dfarley1/SPOT/CAD/Ping Sensor/ultrasonic.JPG

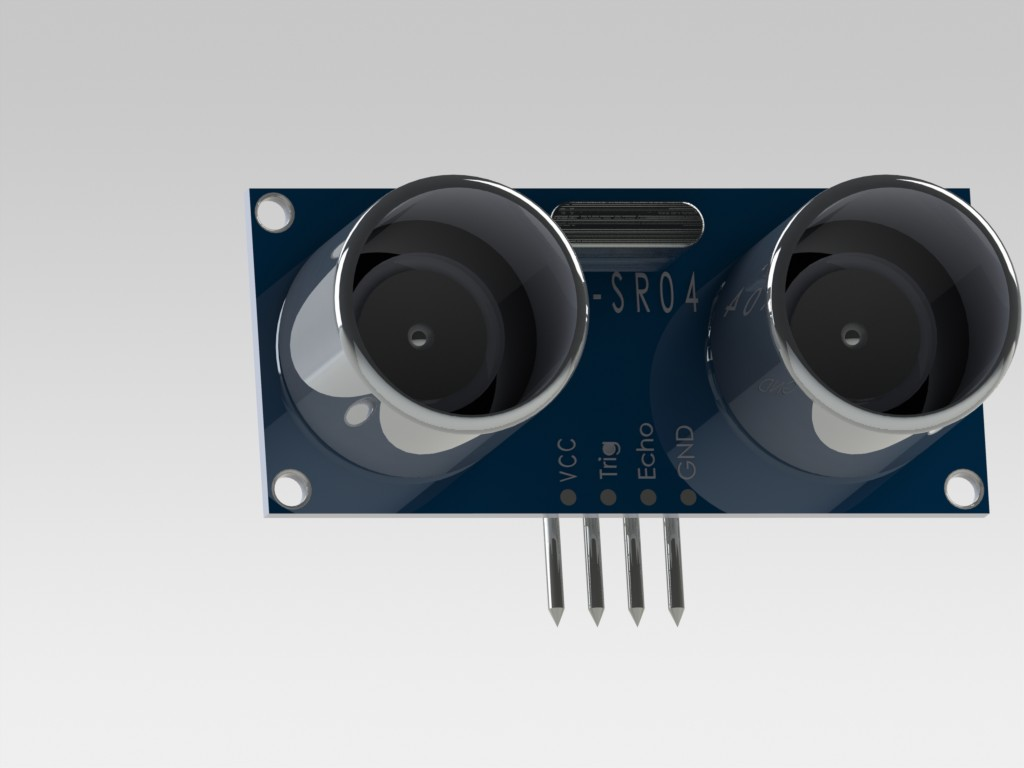
CAD/Ping Sensor/ultrasonic.JPG
