dfarley1/SPOT/CV/Pictures/Leopard/4YFD116.png

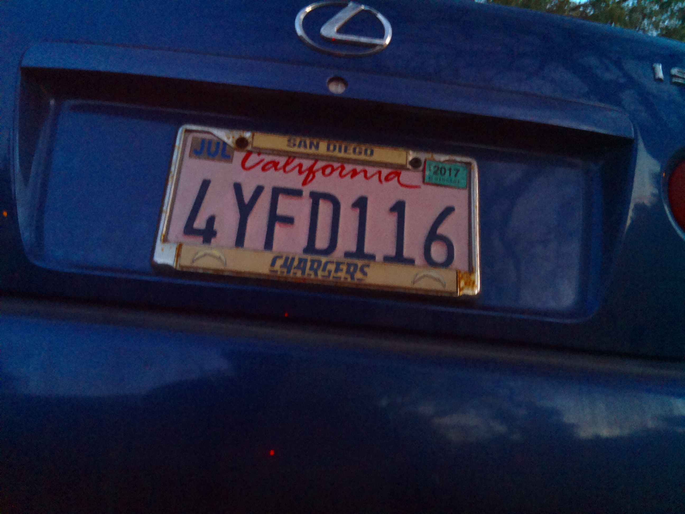
CV/Pictures/Leopard/4YFD116.png
