dfarley1/SPOT/CV/Pictures/Leopard/7FHW353.png

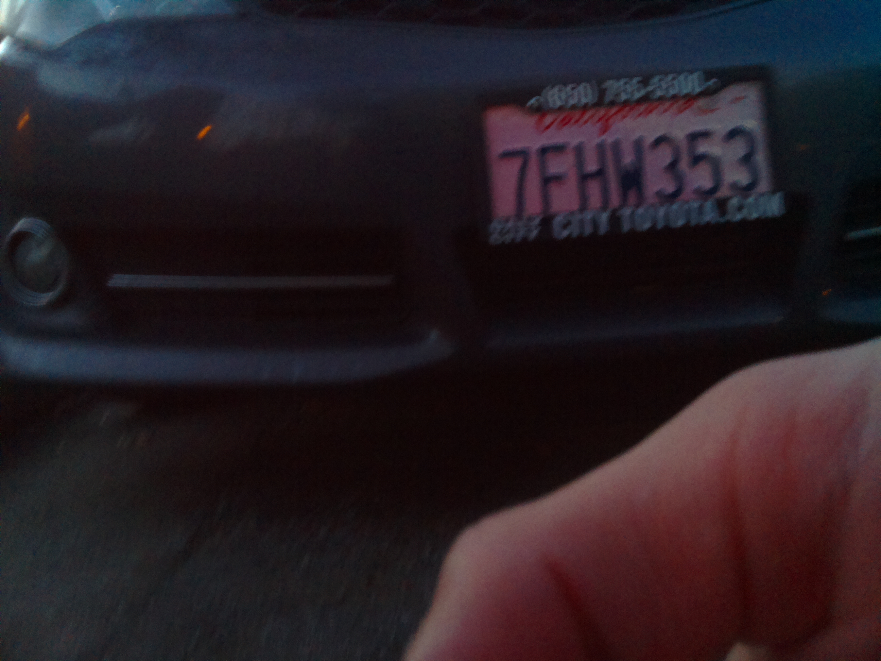
CV/Pictures/Leopard/7FHW353.png
