dfarley1/SPOT/CV/Pictures/Leopard/7FHW353_2.png

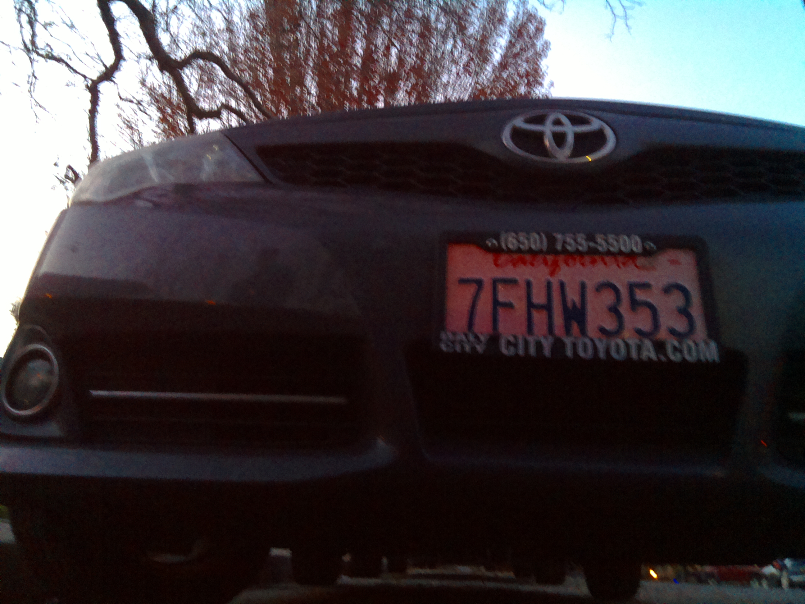
CV/Pictures/Leopard/7FHW353_2.png
