dfarley1/SPOT/CV/Pictures/Leopard/7PYU523.png

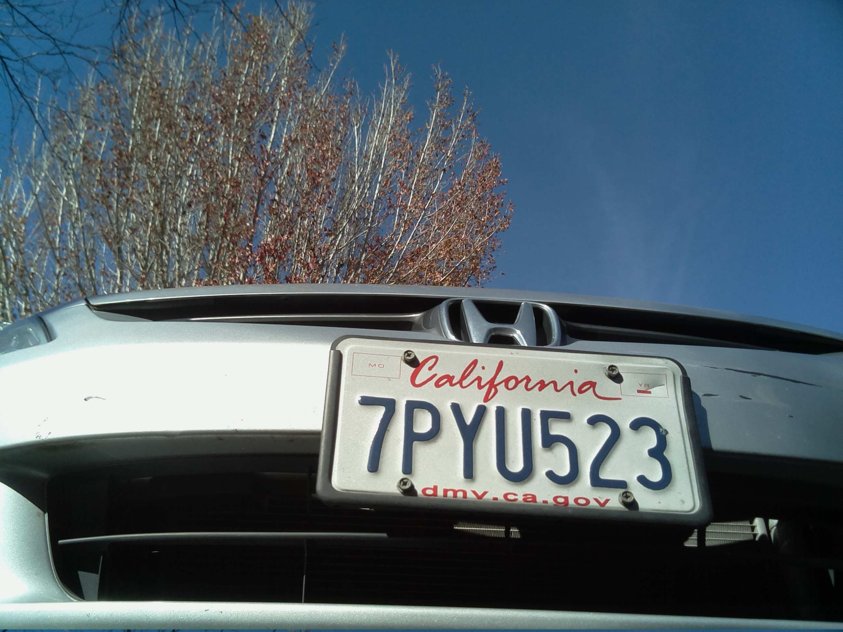
CV/Pictures/Leopard/7PYU523.png
