dfarley1/SPOT/CV/Pictures/Leopard/7PYU523_2.png

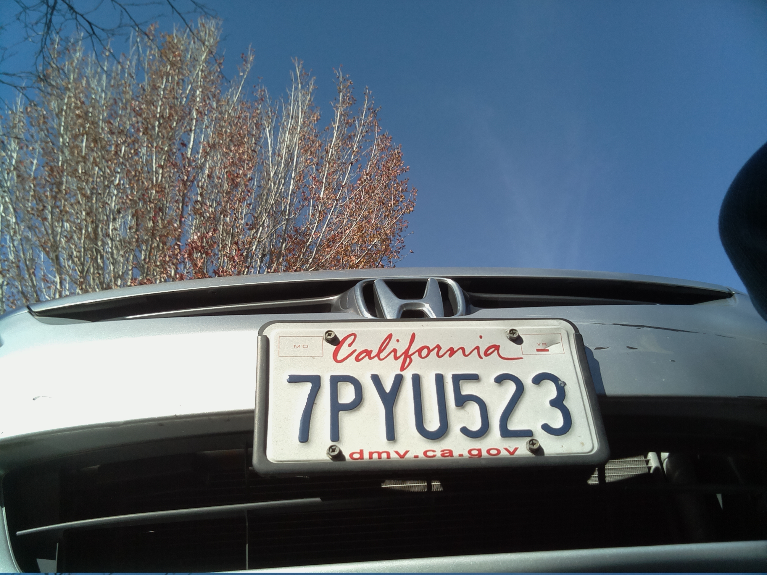
CV/Pictures/Leopard/7PYU523_2.png
