dfarley1/SPOT/CV/Pictures/Leopard/7PYU523_4.png

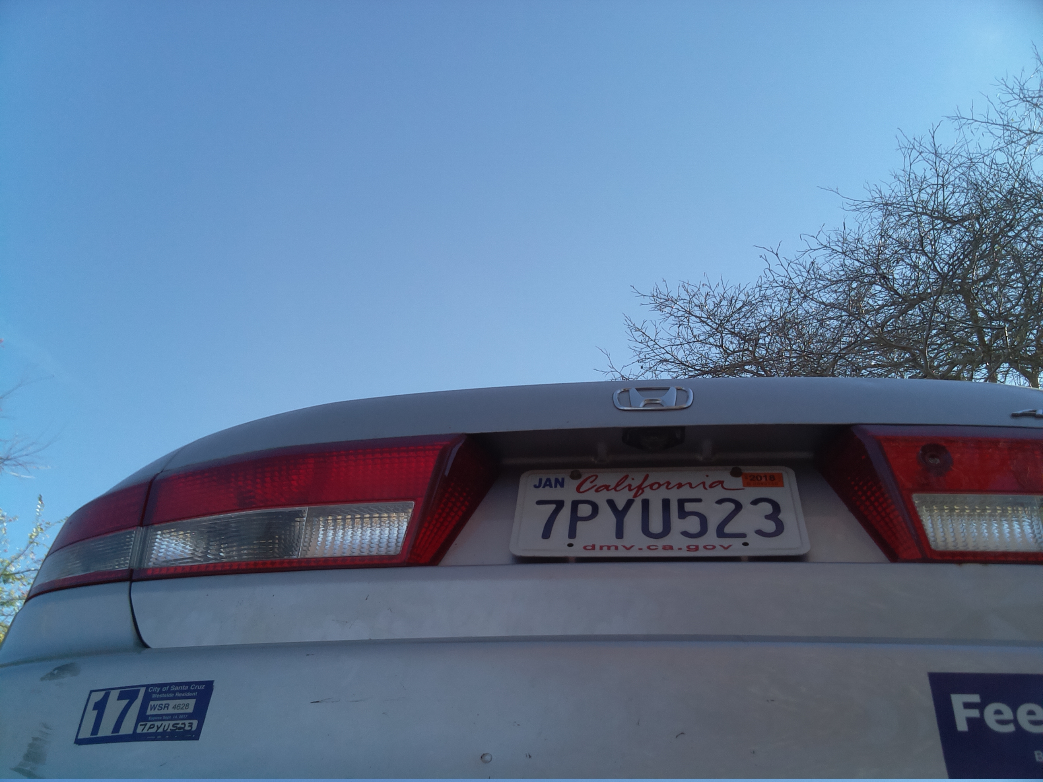
CV/Pictures/Leopard/7PYU523_4.png
