dfarley1/SPOT/CV/Pictures/Leopard/7PYU523_5.png

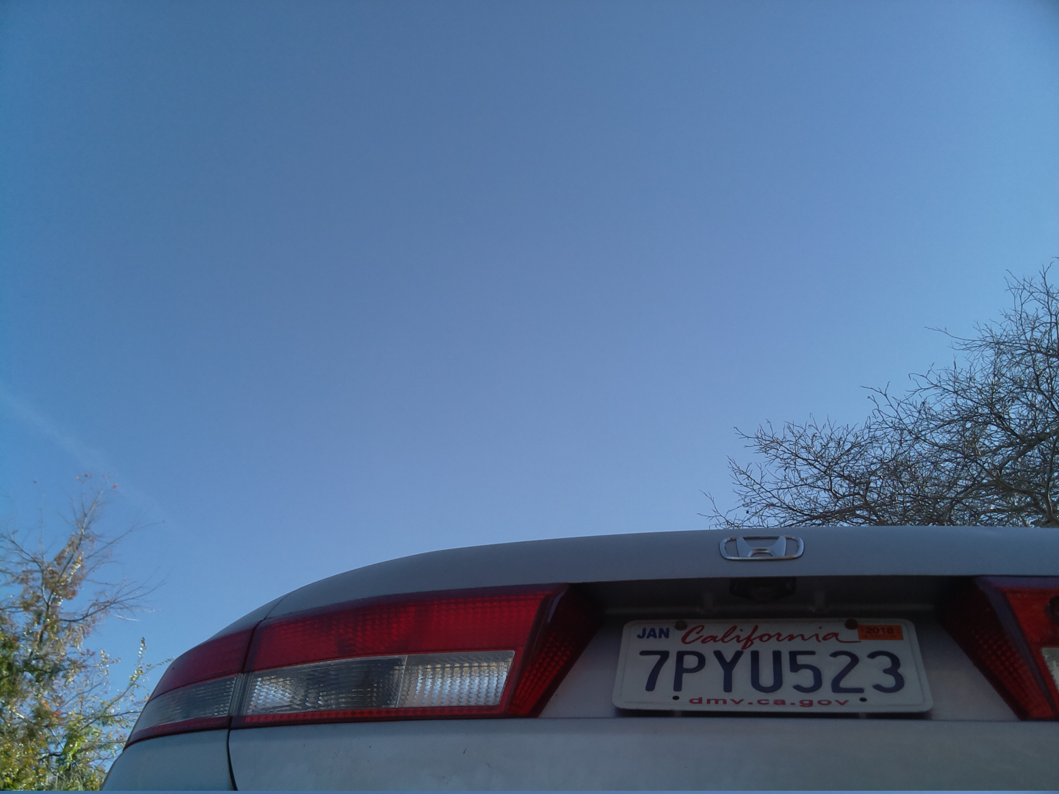
CV/Pictures/Leopard/7PYU523_5.png
