dfarley1/SPOT/Doc/pictures/FileOrganizer.png

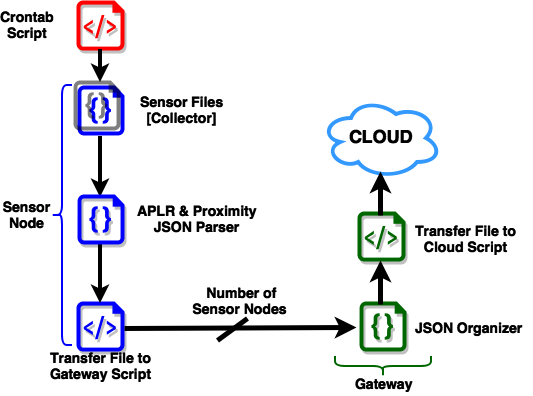
Doc/pictures/FileOrganizer.png
