dfarley1/SPOT/WebApp/bkup/parking-map-111916-1.png

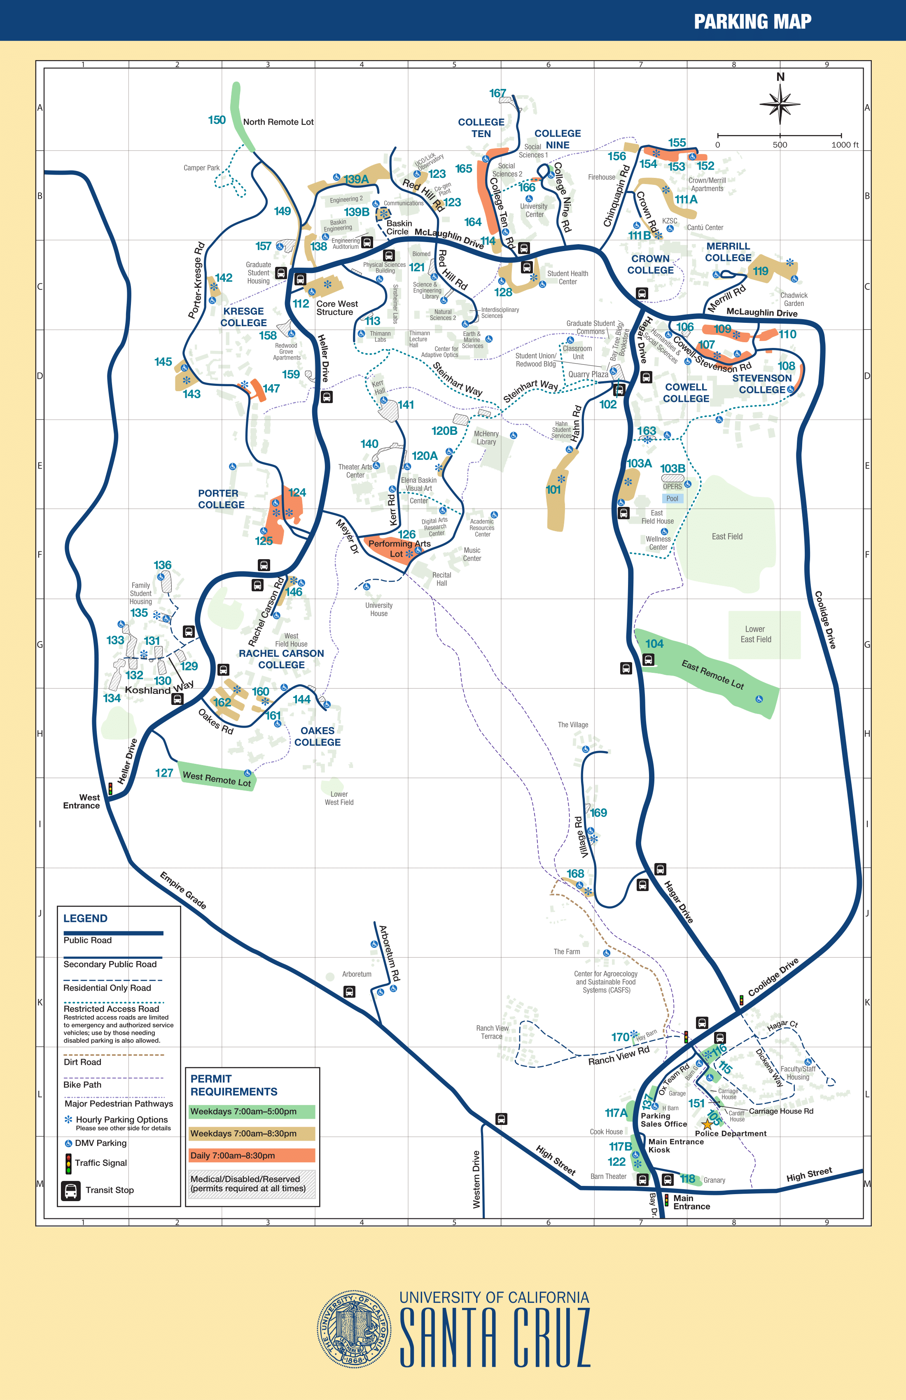
WebApp/bkup/parking-map-111916-1.png
