dfarley1/SPOT/CAD/Box/SHELF.SLDPRT

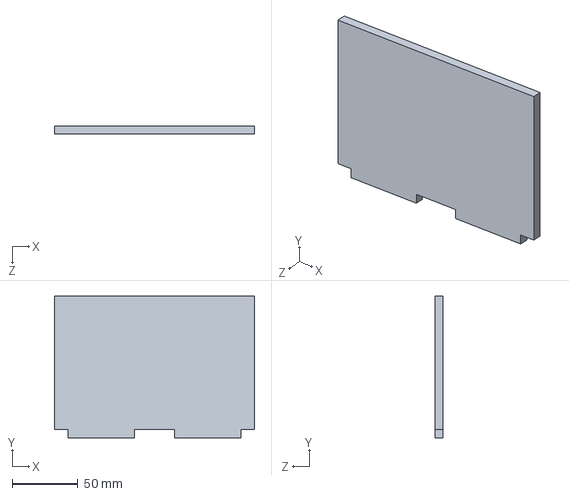
[picture p47: CAD file, 2017-02-27]
CAD/Box/SHELF.SLDPRT
152.4 x 108.0 x 6.35 mm
