dfarley1/SPOT/CAD/Camera/OVA5647_Lens.SLDPRT

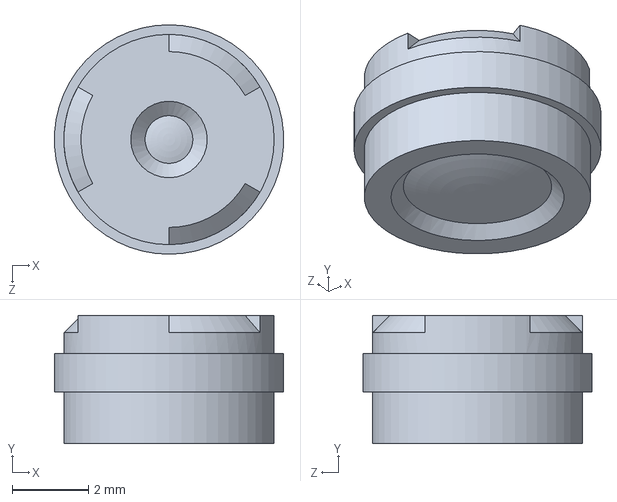
[picture p48: CAD file, 2017-02-09]
CAD/Camera/OVA5647_Lens.SLDPRT
5.99 x 3.35 x 6.00 mm
