dfarley1/SPOT/CAD/Model A/3D print v3/bottomsmalllide.STL

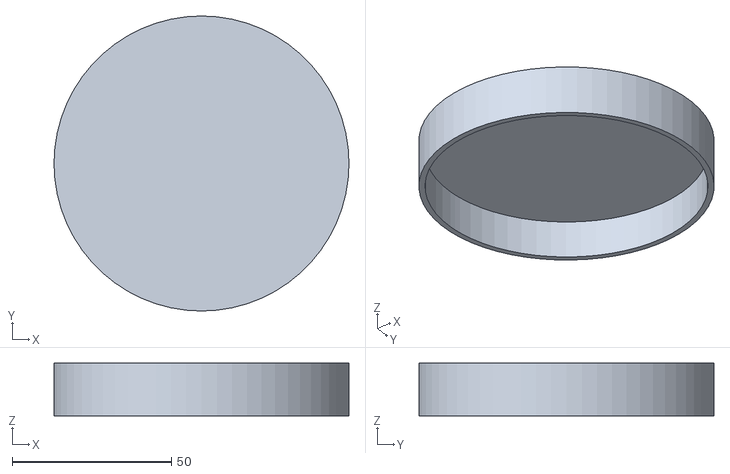
[picture p49: CAD file, 2017-05-10]
CAD/Model A/3D print v3/bottomsmalllide.STL
92.7 x 92.7 x 16.5
