dfarley1/SPOT/CAD/Model A/backwallspacer.SLDPRT

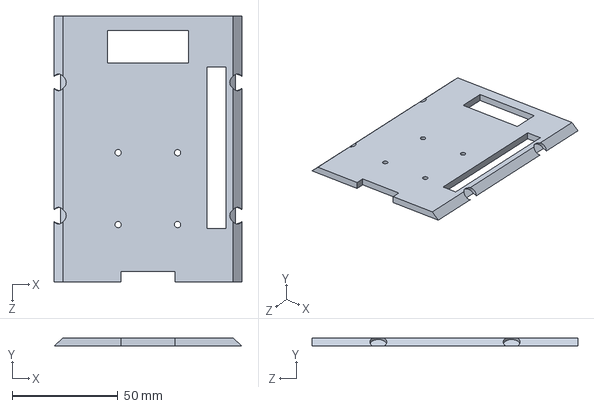
[picture p50: CAD file, 2017-05-24]
CAD/Model A/backwallspacer.SLDPRT
88.8 x 3.81 x 125.7 mm
