dfarley1/SPOT/CAD/Ping Sensor/Ultra/E&T.SLDPRT

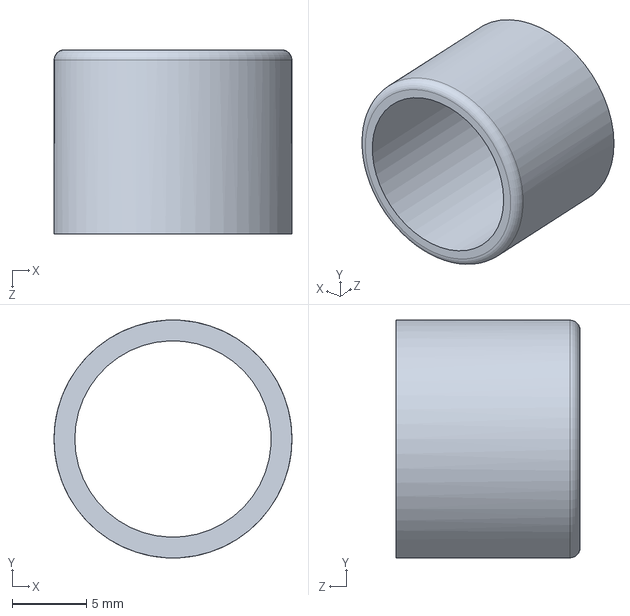
[picture p51: CAD file, 2017-02-09]
CAD/Ping Sensor/Ultra/E&T.SLDPRT
16.0 x 16.0 x 12.4 mm
