dfarley1/SPOT/CAD/Ping Sensor/Ultraconico.SLDPRT

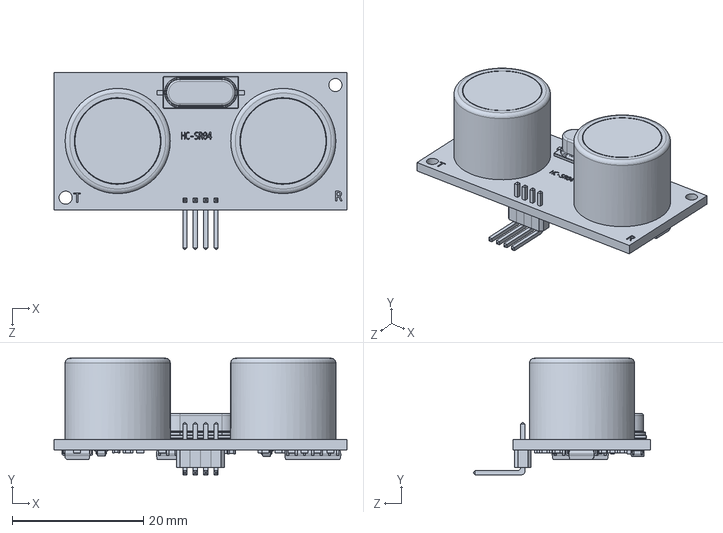
[picture p52: CAD file, 2017-02-09]
CAD/Ping Sensor/Ultraconico.SLDPRT
44.6 x 17.7 x 26.9 mm
