dfarley1/SPOT/CAD/Box/frontpanel.SLDPRT

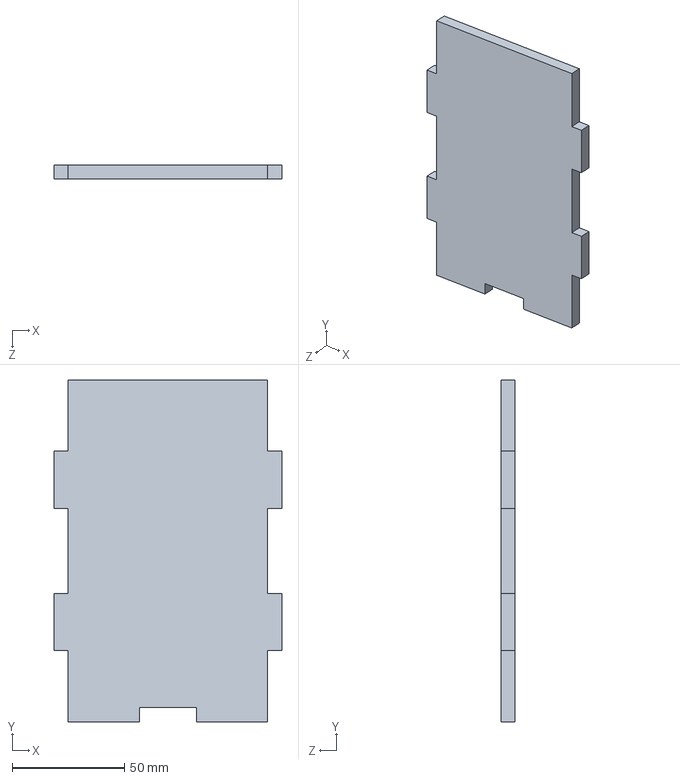
[picture p53: CAD file, 2017-02-27]
CAD/Box/frontpanel.SLDPRT
101.6 x 152.4 x 6.35 mm
