dfarley1/SPOT/CAD/Model A/3D print v3/backwalltubesensors.STL

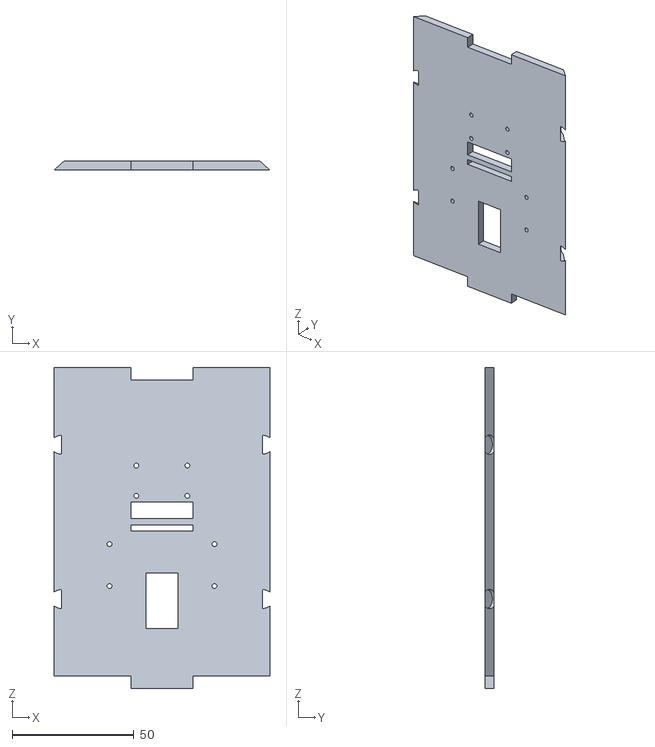
[picture p54: CAD file, 2017-05-10]
CAD/Model A/3D print v3/backwalltubesensors.STL
88.8 x 3.81 x 132.0
