dfarley1/SPOT/CAD/Ping Sensor/Ultra/PCB.SLDPRT

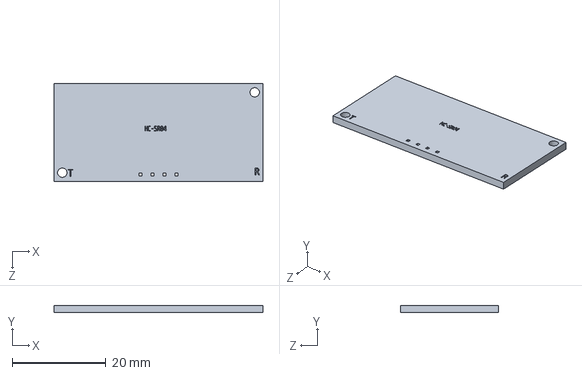
[picture p55: CAD file, 2017-02-09]
CAD/Ping Sensor/Ultra/PCB.SLDPRT
44.6 x 1.60 x 20.9 mm
