dfarley1/SPOT/CAD/Box/box.SLDPRT

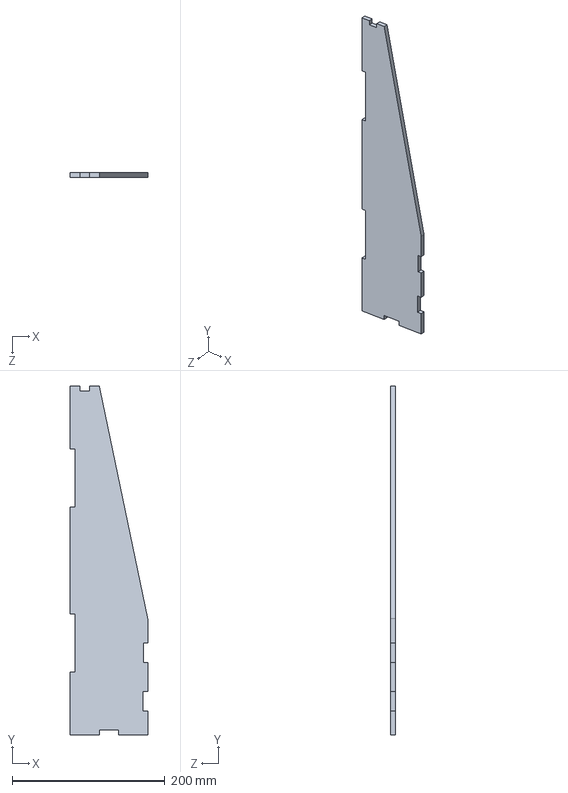
[picture p56: CAD file, 2017-02-27]
CAD/Box/box.SLDPRT
101.6 x 457.2 x 6.35 mm
