dfarley1/SPOT/CAD/Camera/OVA5647_Housing.SLDPRT

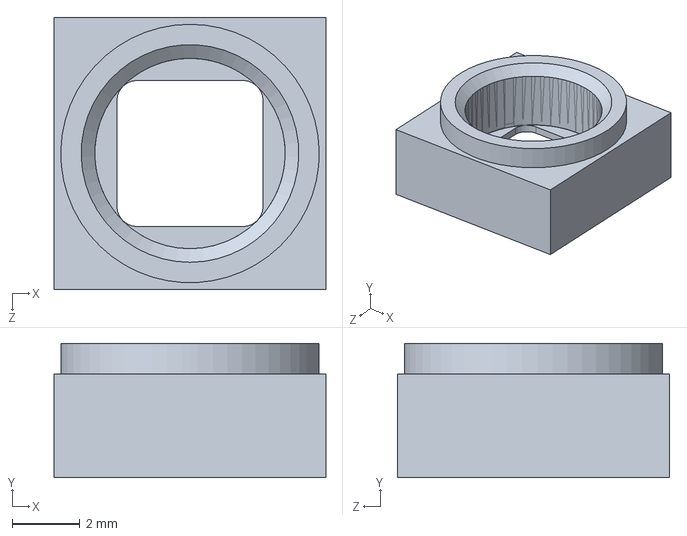
[picture p57: CAD file, 2017-02-09]
CAD/Camera/OVA5647_Housing.SLDPRT
8.00 x 3.95 x 8.00 mm
