dfarley1/SPOT/CAD/Curb/Part1.SLDPRT

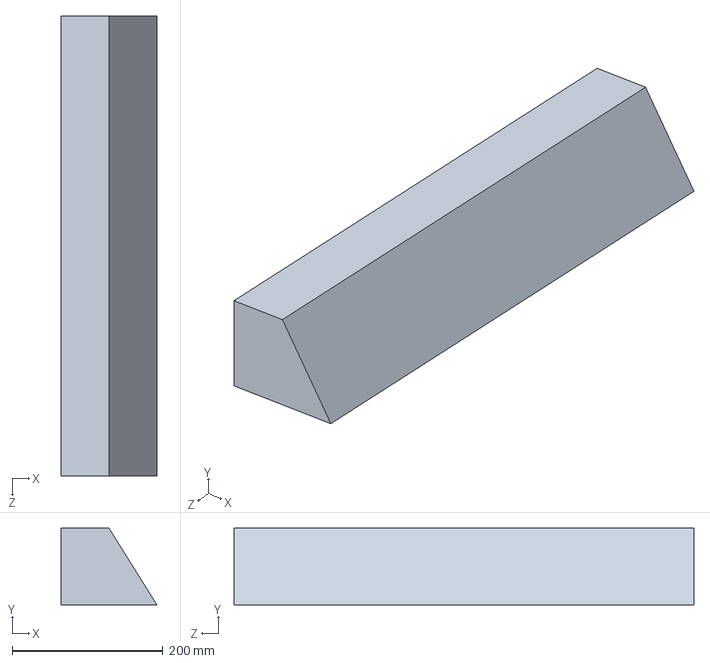
[picture p58: CAD file, 2017-02-09]
CAD/Curb/Part1.SLDPRT
127.0 x 101.6 x 609.6 mm
