dfarley1/SPOT/CAD/Model A/3D print v3/tubepiv2.STL

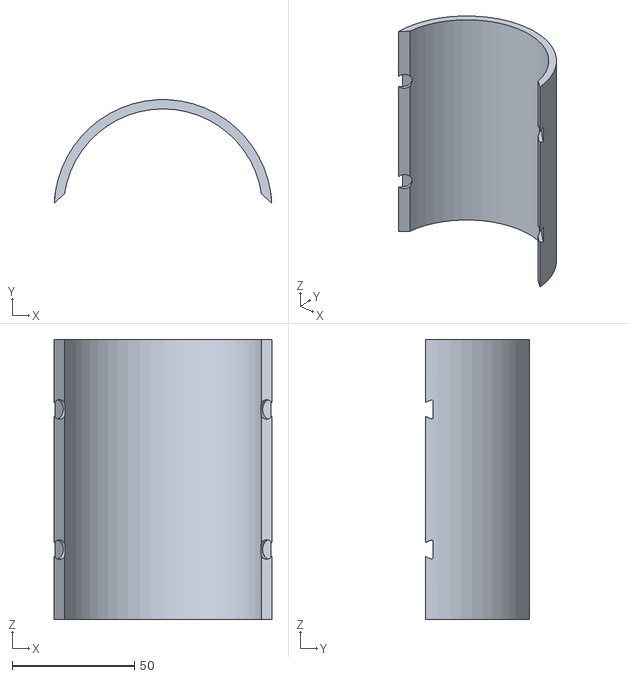
[picture p59: CAD file, 2017-05-10]
CAD/Model A/3D print v3/tubepiv2.STL
88.8 x 42.3 x 114.3
