dfarley1/SPOT/CAD/Ping Sensor/Ultra/pinB.SLDPRT

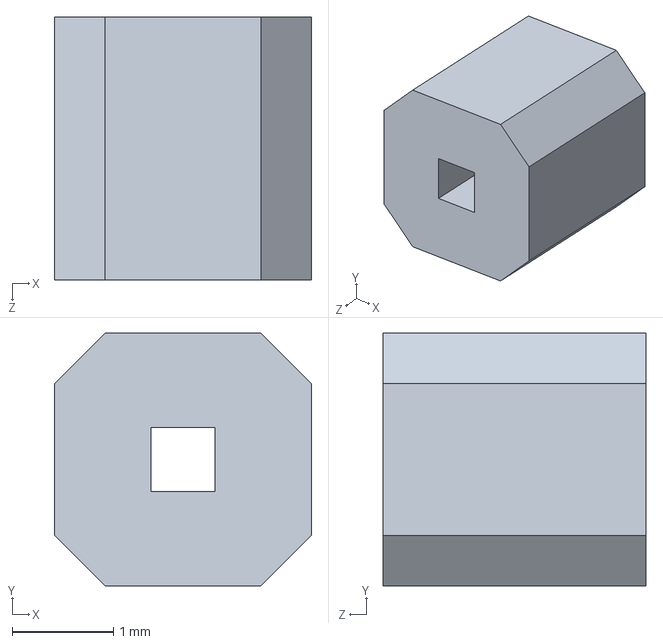
[picture p60: CAD file, 2017-02-09]
CAD/Ping Sensor/Ultra/pinB.SLDPRT
2.54 x 2.50 x 2.60 mm
