dfarley1/SPOT/CAD/Box/bottompanel.SLDPRT

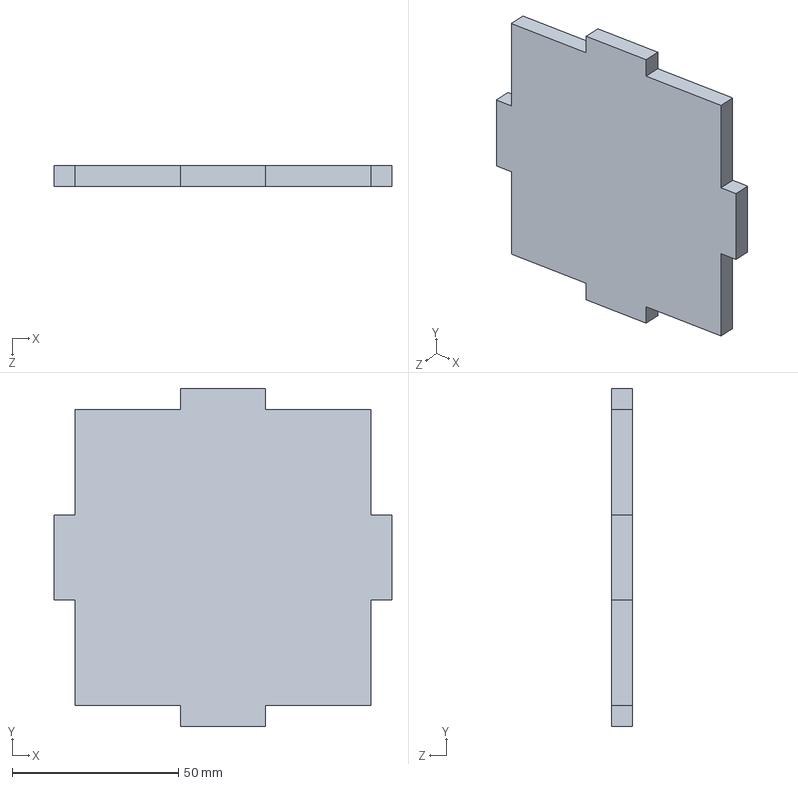
[picture p61: CAD file, 2017-02-27]
CAD/Box/bottompanel.SLDPRT
101.6 x 101.6 x 6.35 mm
