dfarley1/SPOT/CAD/Camera/RasPi_Camera_Board.SLDPRT

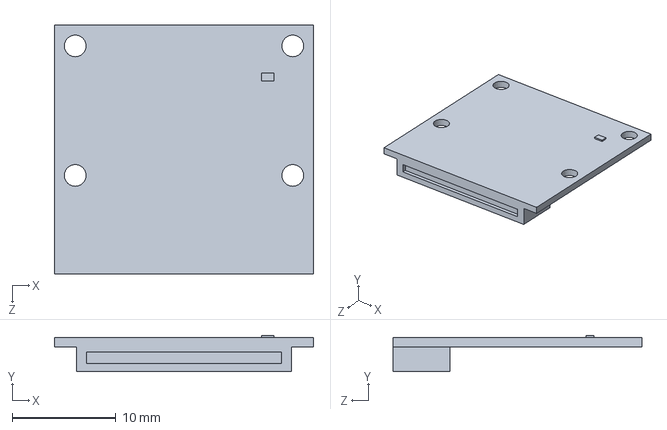
[picture p62: CAD file, 2017-02-09]
CAD/Camera/RasPi_Camera_Board.SLDPRT
25.0 x 3.50 x 24.0 mm
