dfarley1/SPOT/CAD/Curb/backwallcurb.SLDPRT

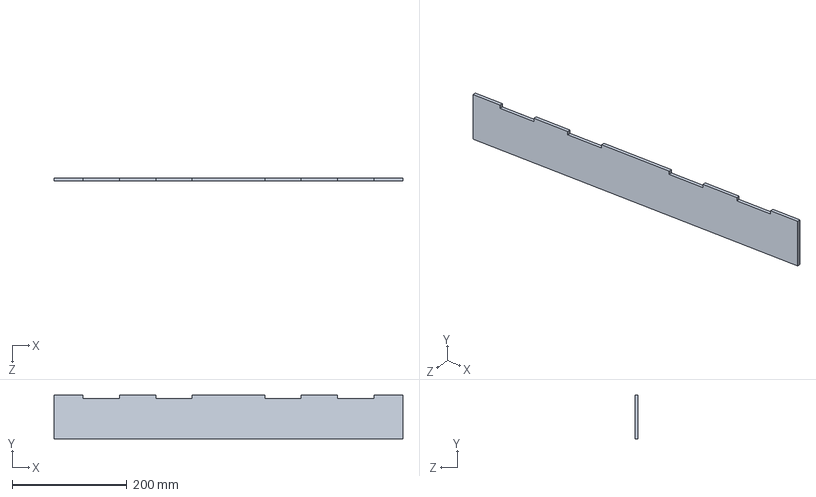
[picture p63: CAD file, 2017-02-09]
CAD/Curb/backwallcurb.SLDPRT
609.6 x 76.2 x 5.59 mm
