dfarley1/SPOT/CAD/Model A/3D print v3/tubepi.STL

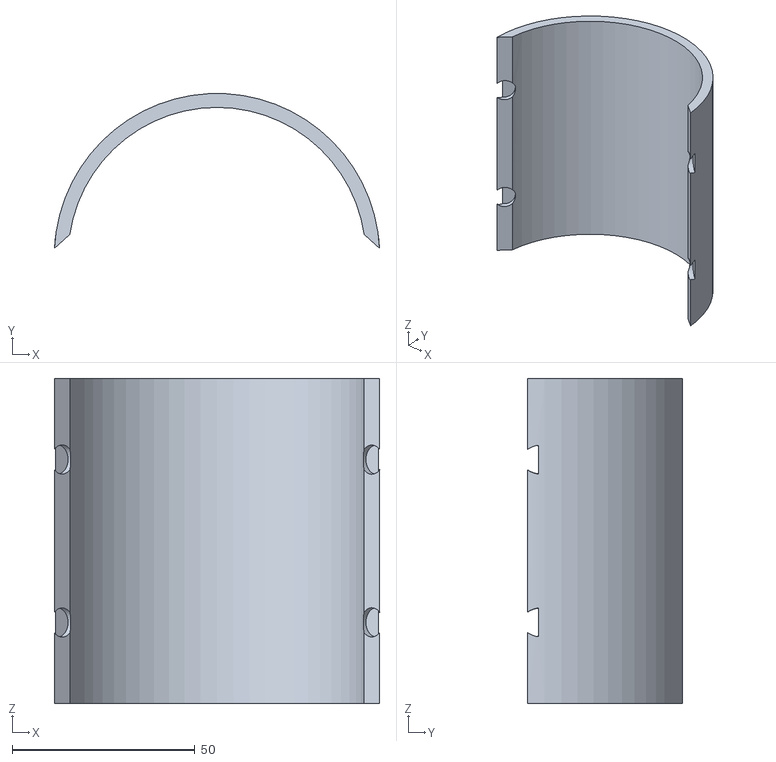
[picture p64: CAD file, 2017-05-10]
CAD/Model A/3D print v3/tubepi.STL
88.8 x 42.3 x 88.9
