dfarley1/SPOT/CAD/Ping Sensor/Ultra/User Library-ABLS2.SLDPRT

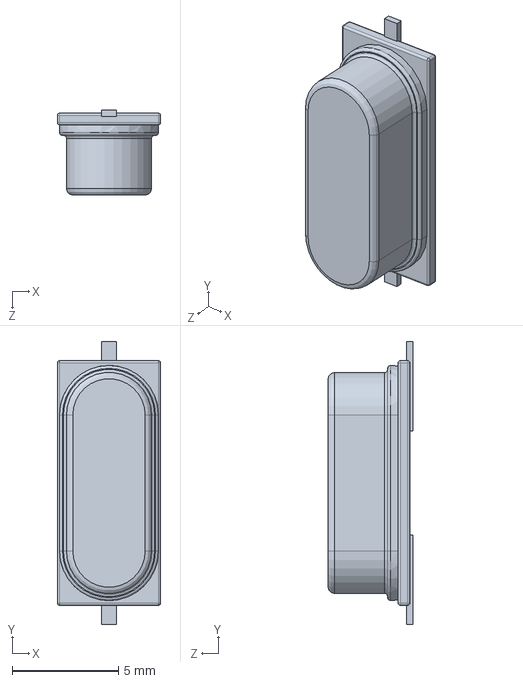
[picture p65: CAD file, 2017-02-09]
CAD/Ping Sensor/Ultra/User Library-ABLS2.SLDPRT
4.85 x 13.3 x 4.00 mm
