dfarley1/SPOT/CAD/Box/top panel.SLDPRT

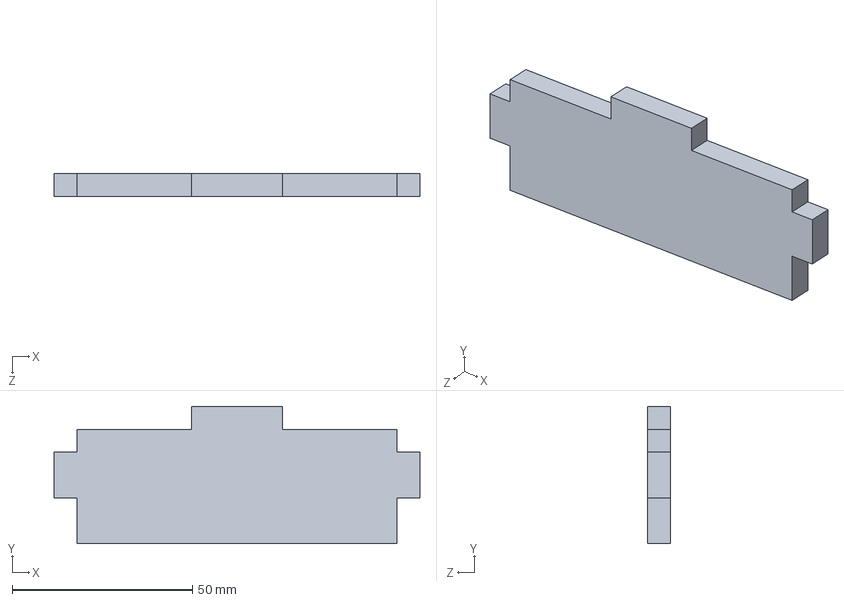
[picture p66: CAD file, 2017-02-27]
CAD/Box/top panel.SLDPRT
101.6 x 38.1 x 6.35 mm
