dfarley1/SPOT/CAD/Camera/OVA5647_Pigtail.SLDPRT

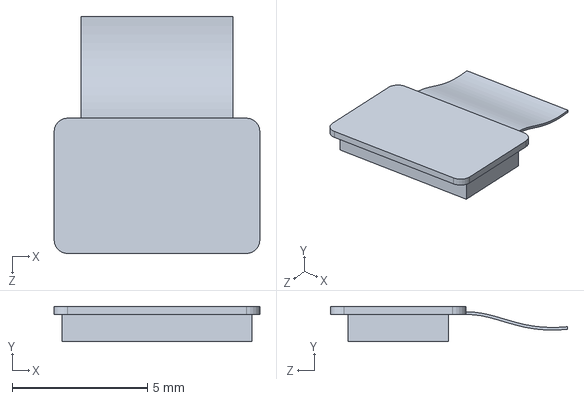
[picture p67: CAD file, 2017-02-09]
CAD/Camera/OVA5647_Pigtail.SLDPRT
7.60 x 1.30 x 8.75 mm
