dfarley1/SPOT/CAD/Model A/3D print v3/backwalltubev2.STL

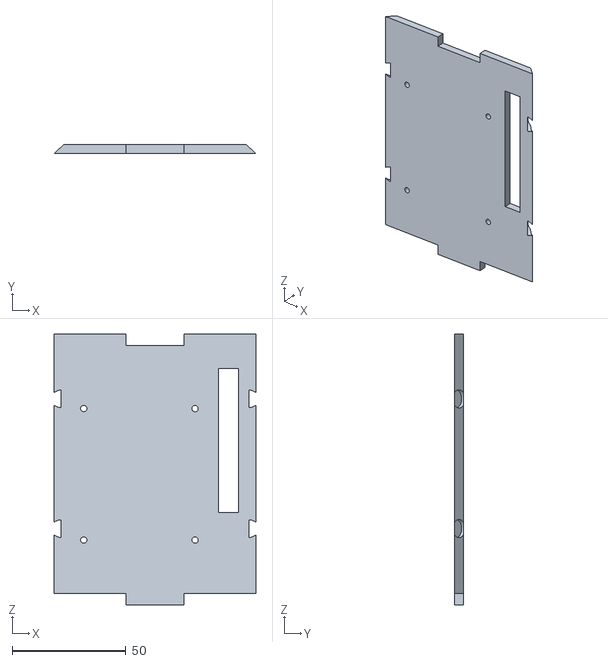
[picture p68: CAD file, 2017-05-10]
CAD/Model A/3D print v3/backwalltubev2.STL
88.8 x 3.81 x 119.4
