dfarley1/SPOT/CAD/Ping Sensor/Ultra/pinA.SLDPRT

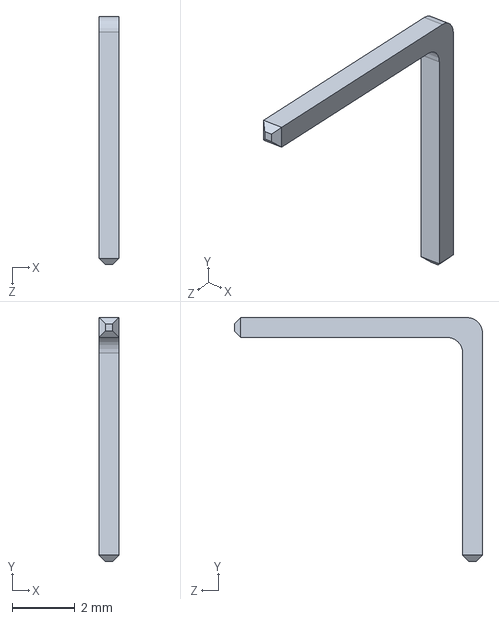
[picture p69: CAD file, 2017-02-09]
CAD/Ping Sensor/Ultra/pinA.SLDPRT
0.636 x 7.80 x 7.94 mm
