dfarley1/SPOT/CAD/Curb/topcurb.SLDPRT

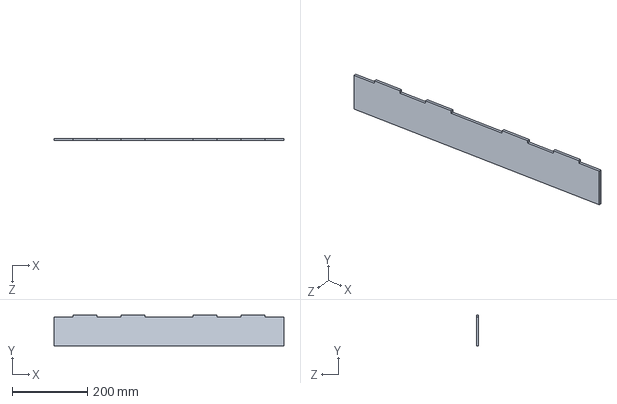
[picture p70: CAD file, 2017-02-09]
CAD/Curb/topcurb.SLDPRT
609.6 x 81.8 x 5.59 mm
