dfarley1/SPOT/CAD/Model A/3D print v3/backwalltube.STL

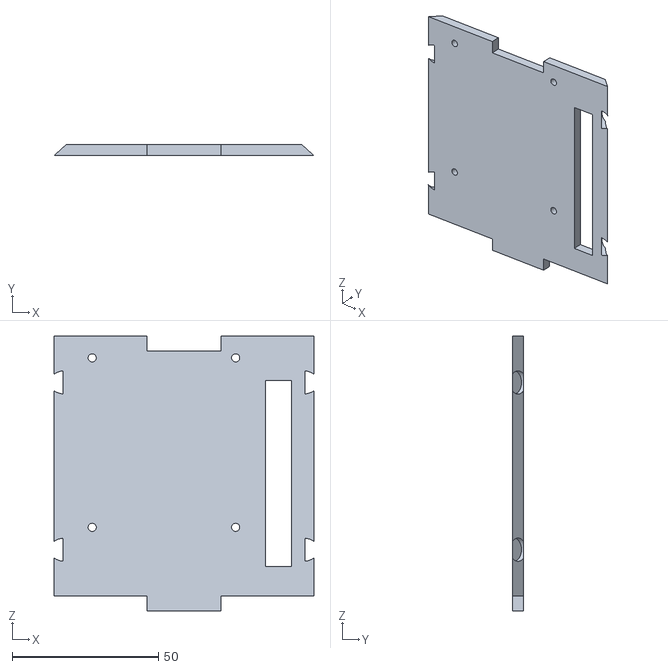
[picture p71: CAD file, 2017-05-10]
CAD/Model A/3D print v3/backwalltube.STL
88.8 x 3.81 x 94.0
