dfarley1/SPOT/CAD/Ping Sensor/Ultra/User Library-SOIC14-150-1.SLDPRT

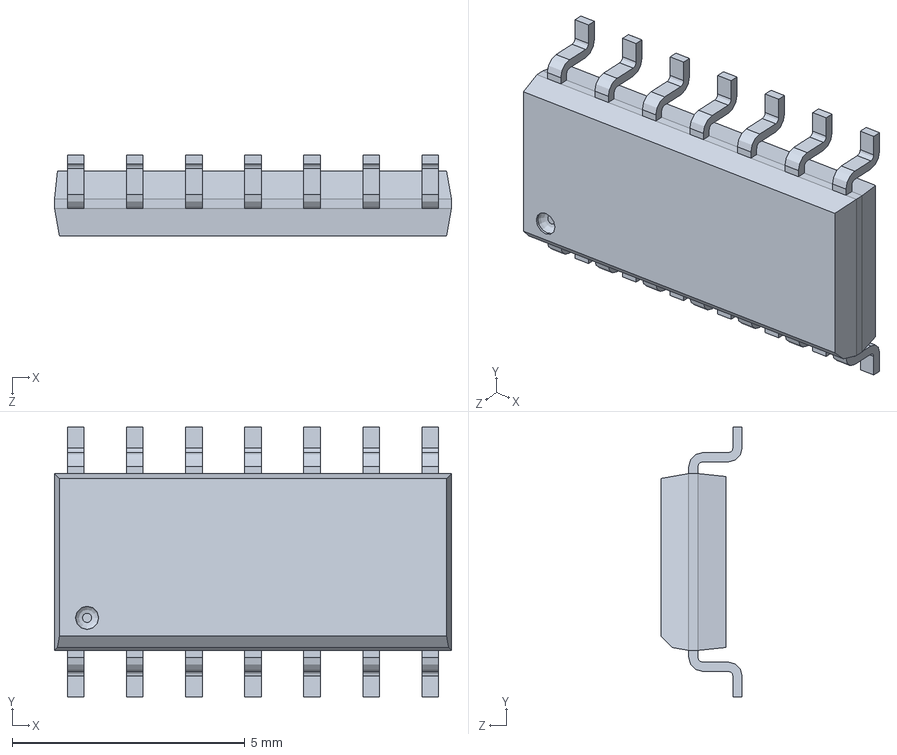
[picture p72: CAD file, 2017-02-09]
CAD/Ping Sensor/Ultra/User Library-SOIC14-150-1.SLDPRT
8.53 x 5.80 x 1.75 mm
