dfarley1/SPOT/CAD/Curb/2x4.SLDPRT

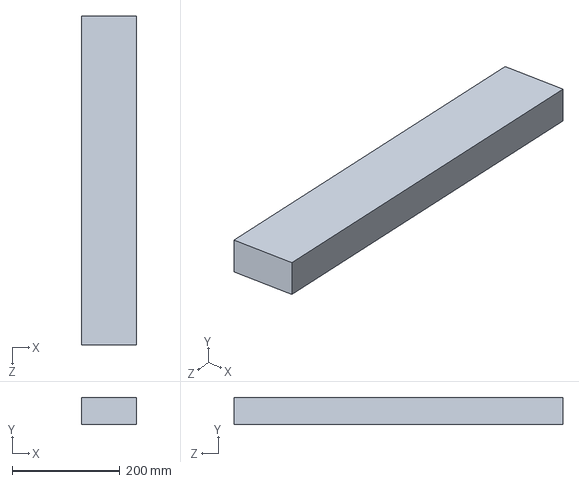
[picture p73: CAD file, 2017-01-30]
CAD/Curb/2x4.SLDPRT
101.6 x 50.8 x 609.6 mm
