dfarley1/SPOT/CAD/Model A/3D print v3/lid.STL

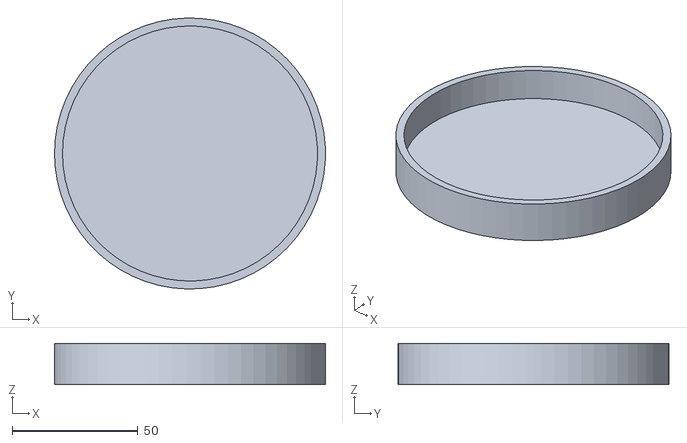
[picture p74: CAD file, 2017-05-04]
CAD/Model A/3D print v3/lid.STL
108.0 x 107.9 x 16.5
