dfarley1/SPOT/CAD/Model A/3D printed V4/tubespacerv2.STL

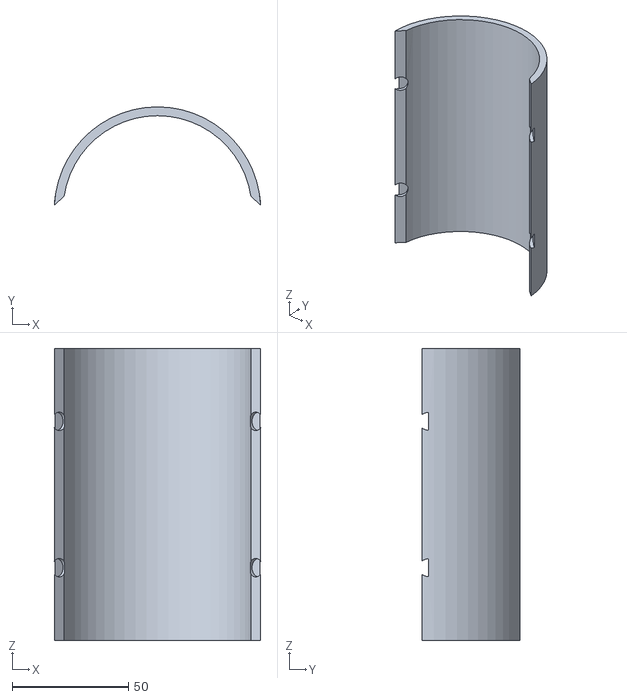
[picture p75: CAD file, 2017-05-10]
CAD/Model A/3D printed V4/tubespacerv2.STL
88.8 x 42.3 x 125.7
