dfarley1/SPOT/CAD/Ping Sensor/Ultra/0404_r_1620019.sldprt

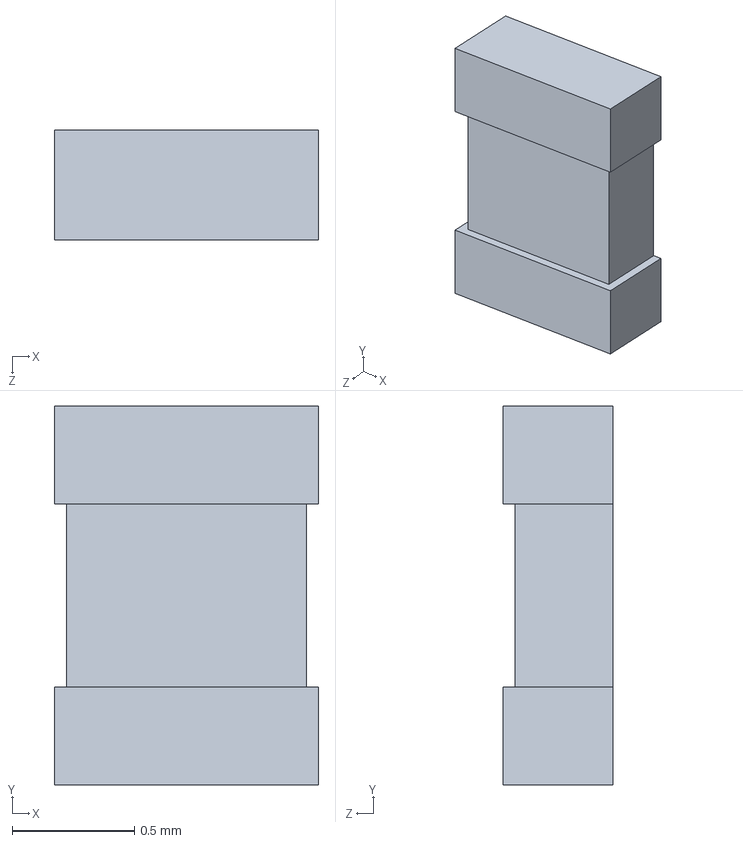
[picture p76: CAD file, 2017-02-09]
CAD/Ping Sensor/Ultra/0404_r_1620019.sldprt
1.08 x 1.55 x 0.45 mm
