dfarley1/SPOT/CAD/Ping Sensor/Ultra/0402c_2320560.sldprt

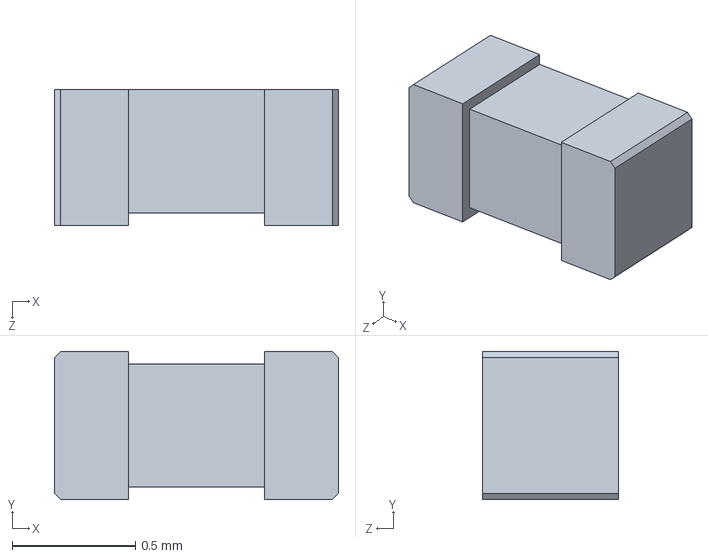
[picture p77: CAD file, 2017-02-09]
CAD/Ping Sensor/Ultra/0402c_2320560.sldprt
1.15 x 0.6 x 0.55 mm
