dfarley1/SPOT/CAD/Box/Parking Stopper.SLDPRT

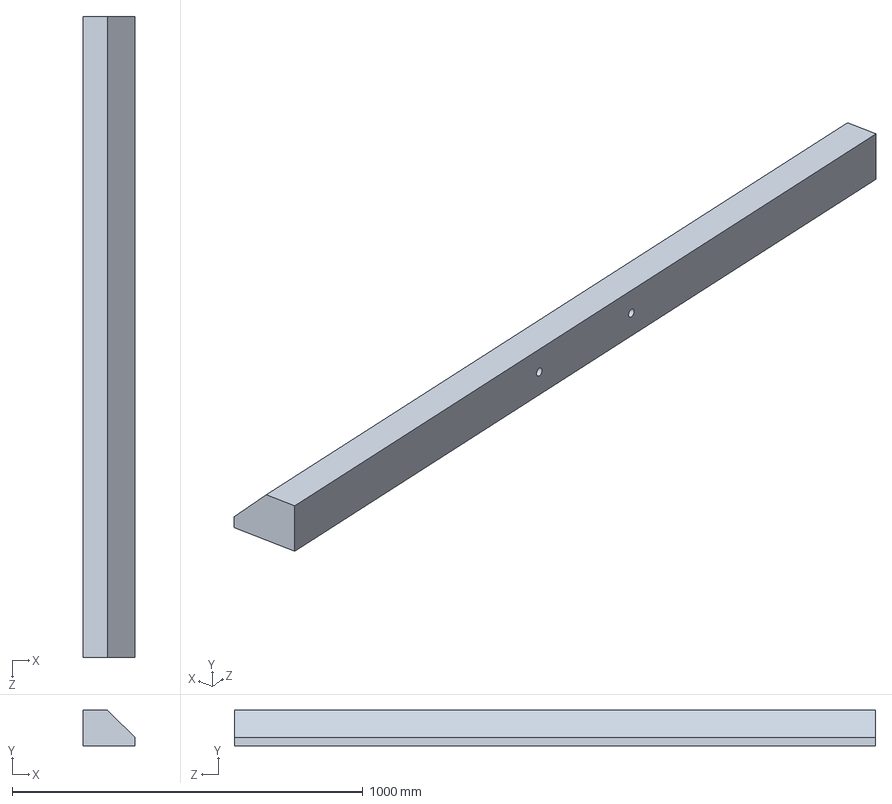
[picture p78: CAD file, 2017-01-18]
CAD/Box/Parking Stopper.SLDPRT
149.2 x 101.6 x 1828.8 mm
