dfarley1/SPOT/CAD/Ping Sensor/Ultra/HeaderMalePart.SLDPRT

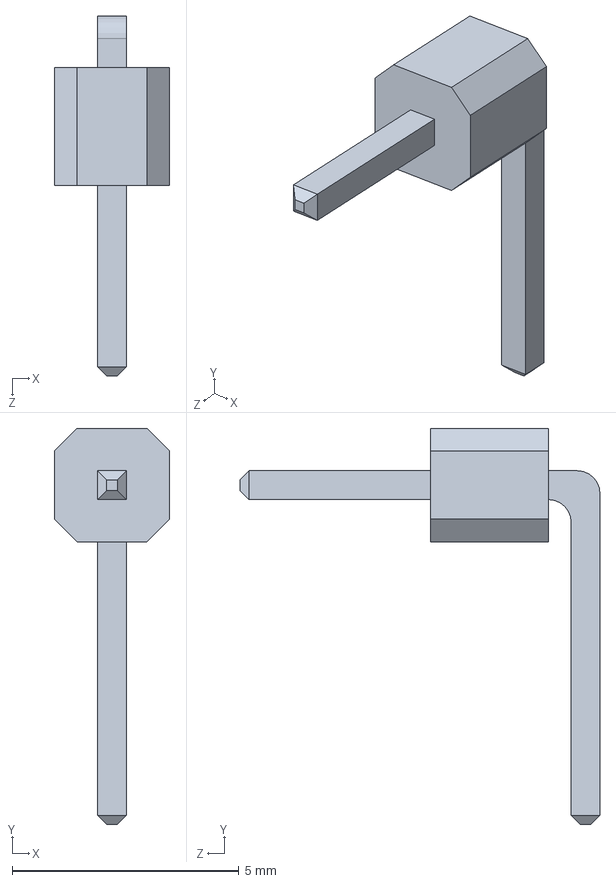
[picture p79: CAD file, 2017-02-09]
CAD/Ping Sensor/Ultra/HeaderMalePart.SLDPRT
2.54 x 8.73 x 7.94 mm
