dfarley1/SPOT/CAD/Model A/3D print v3/backwallspacetopr.STL

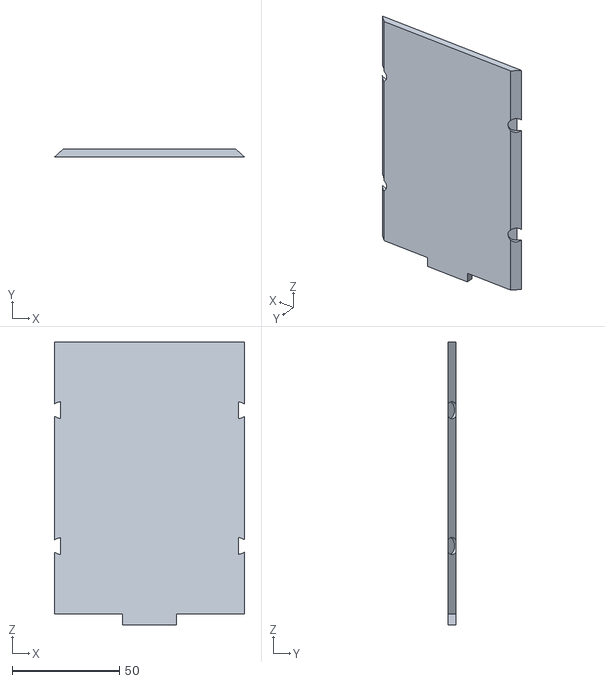
[picture p80: CAD file, 2017-05-04]
CAD/Model A/3D print v3/backwallspacetopr.STL
88.8 x 3.81 x 132.1
