dfarley1/SPOT/CAD/Ping Sensor/Ultra/User Library-SC70-5-1.SLDPRT

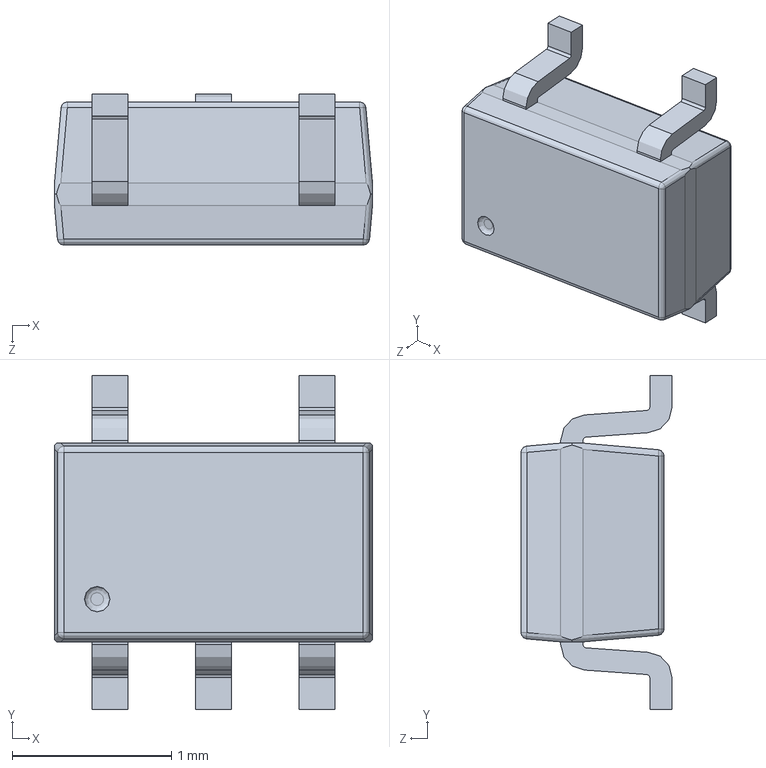
[picture p81: CAD file, 2017-02-09]
CAD/Ping Sensor/Ultra/User Library-SC70-5-1.SLDPRT
2.00 x 2.10 x 0.95 mm
