dfarley1/SPOT/CAD/Ping Sensor/Ultra/HeaderFemale.SLDPRT

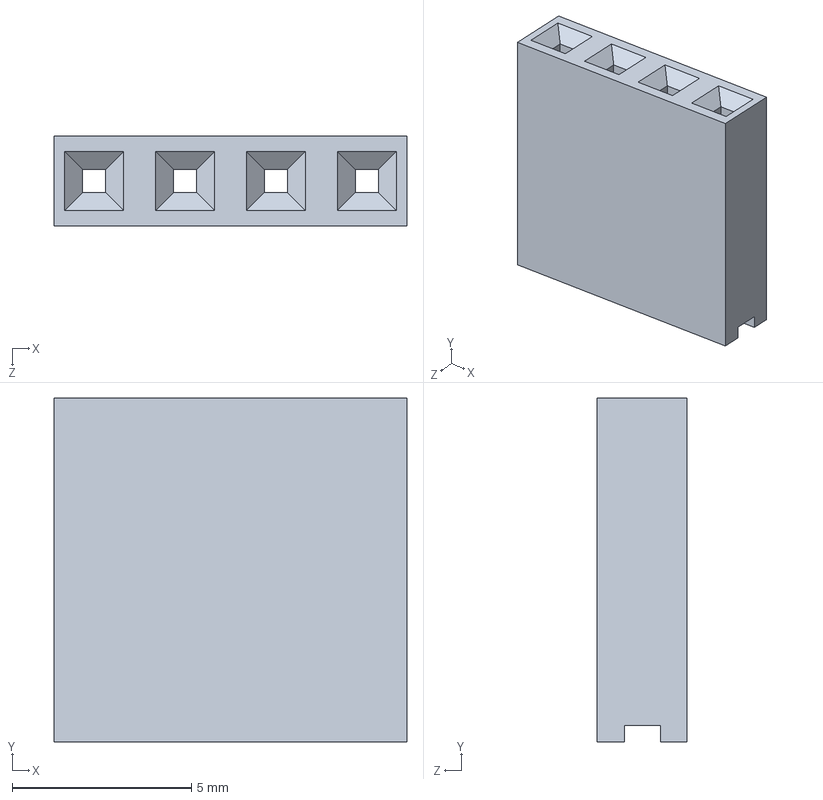
[picture p82: CAD file, 2017-02-09]
CAD/Ping Sensor/Ultra/HeaderFemale.SLDPRT
9.86 x 9.60 x 2.50 mm
