dfarley1/SPOT/CAD/Ping Sensor/Ultra/0402r_1430758.sldprt

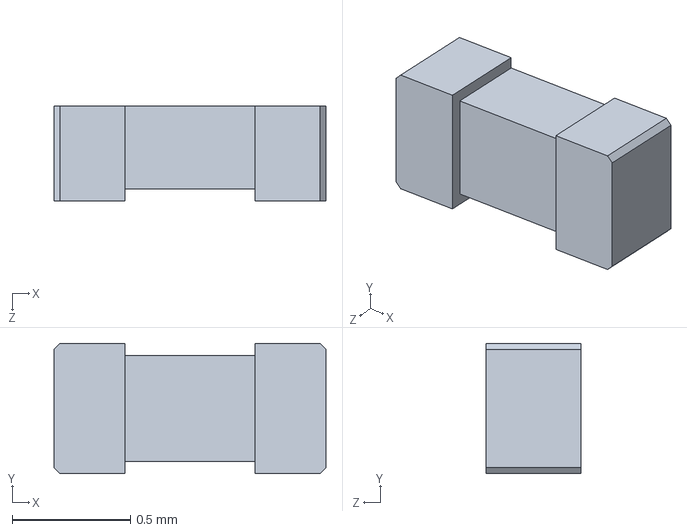
[picture p83: CAD file, 2017-02-09]
CAD/Ping Sensor/Ultra/0402r_1430758.sldprt
1.15 x 0.55 x 0.4 mm
