dfarley1/SPOT/CAD/Model A/rectangle1.SLDPRT

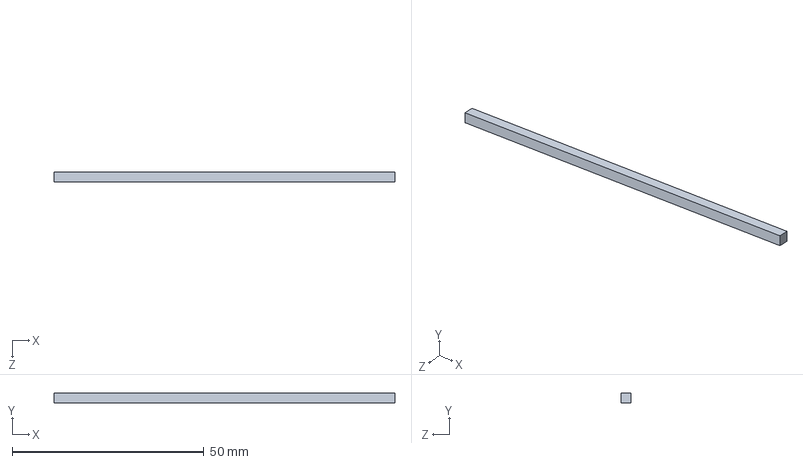
[picture p84: CAD file, 2017-05-04]
CAD/Model A/rectangle1.SLDPRT
88.9 x 2.54 x 2.54 mm
