dfarley1/SPOT/CAD/Model A/rectangle.SLDPRT

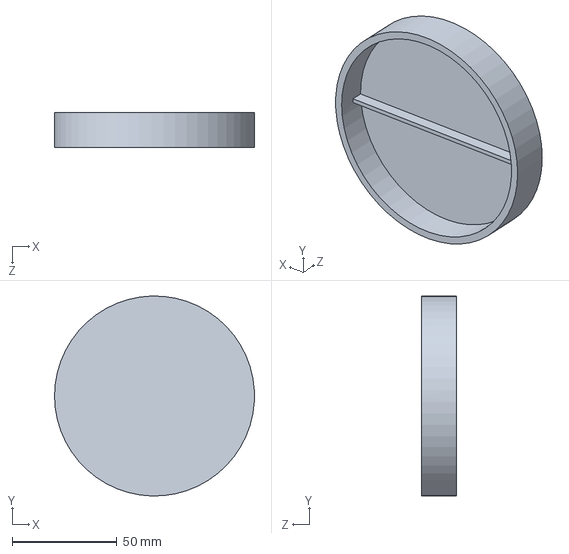
[picture p85: CAD file, 2017-05-04]
CAD/Model A/rectangle.SLDPRT
95.2 x 95.2 x 16.5 mm
