dfarley1/SPOT/CAD/Model A/outertubemiddle.SLDPRT

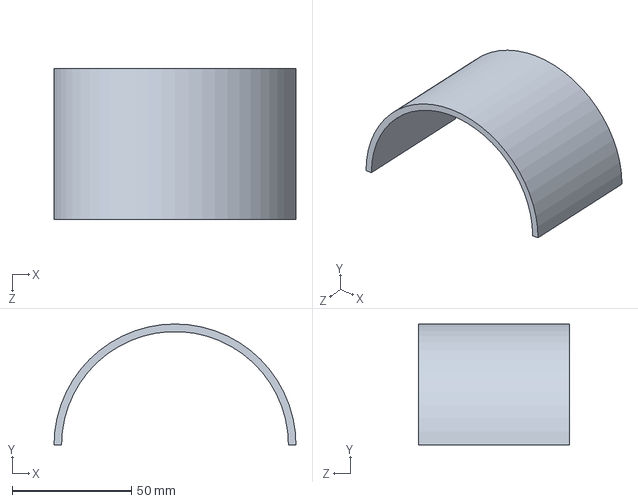
[picture p86: CAD file, 2017-04-19]
CAD/Model A/outertubemiddle.SLDPRT
101.6 x 50.8 x 63.5 mm
