dfarley1/SPOT/CAD/Model A/topoutertube.SLDPRT

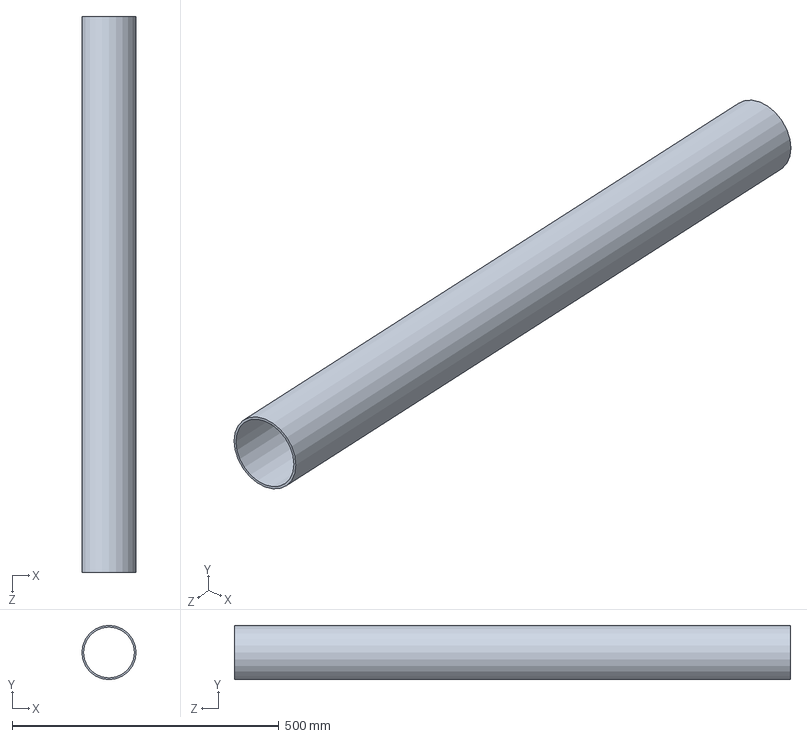
[picture p87: CAD file, 2017-04-19]
CAD/Model A/topoutertube.SLDPRT
101.6 x 101.6 x 1041.4 mm
