dfarley1/SPOT/CAD/Model A/outertube.SLDPRT

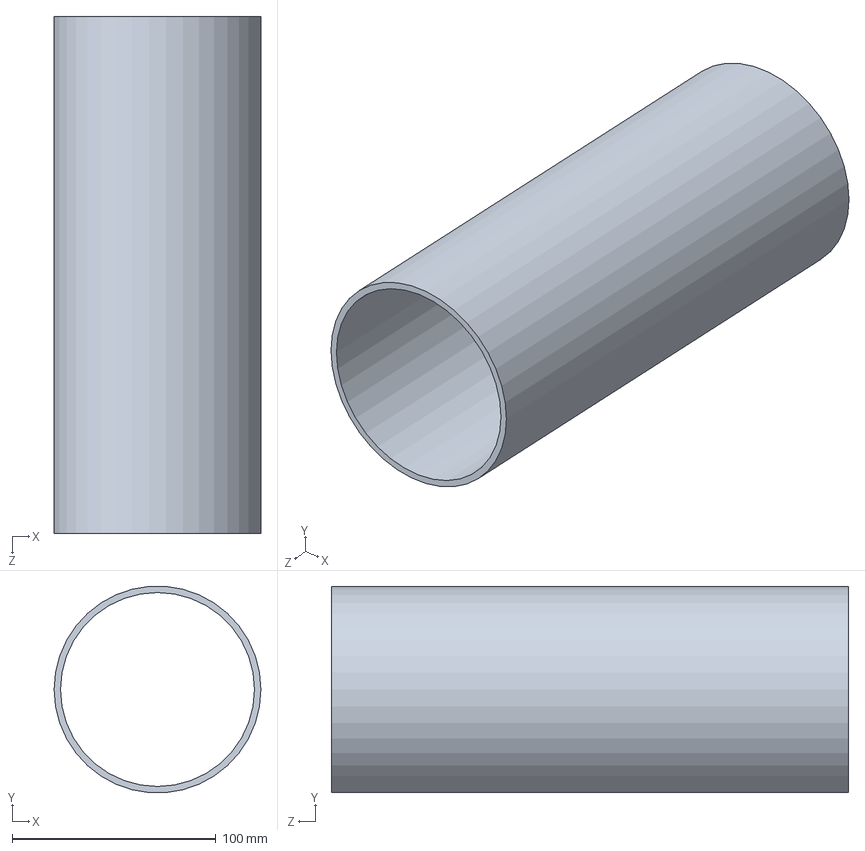
[picture p88: CAD file, 2017-04-19]
CAD/Model A/outertube.SLDPRT
101.6 x 101.3 x 254.0 mm
