dfarley1/SPOT/Cloud/testHttp.py

import requests
import pprint
import pickle
import uuid
import os
import datetime
import binascii
#import RPi.GPIO as GPIO

#base_url = 'http://127.0.0.1:8000/sensor/'
base_url = 'http://alien-walker-157903.appspot.com/sensor/'
get_args = {'sensor_id': '1234'}
get_uuid = {'getuuid'}
#get_args="/sensor/?sensor_id=1234"
#post_args="occ_status=1&occ_since=2017-02-20%2013:34:00&occ_license=4AME671"
cookie_filename = '/home/pi/spot_log/py_cookies.txt'
status_filename = '/home/pi/spot_log/license_log.txt'
timestamp_filename = '/home/pi/spot_log/occupied_since.txt'
uuid_filename = '/home/pi/spot_log/uuid_file.txt'
#cookie_filename = 'py_cookies.txt'

def sensor_GET():
    cookies = loadCookies()
    params = {'sensor_uuid': cookies['sensor_uuid']}
    
    r = requests.get(base_url+"sensor/", params=params)
    
    f = open(uuid_filename, 'w')
    sensor_uuid_hex = uuid.UUID(r.cookies['sensor_uuid']).hex

    s = str(sensor_uuid_hex)
    new_hex = " ".join(s[i:i+2] for i in range(0, len(s),2))
    #hex_s = new_hex[0:12] + new_hex[30:]
    #print(hex_s)
    f.write(new_hex)
    f.close()


    #saveCookies(r.cookies)
    printResponse(r)
    print(uuid_filename)


def sensor_POST():
    #COLOR = 12
    #GPIO.cleanup()
    #GPIO.setmode(GPIO.BCM)
    #GPIO.setup(COLOR, GPIO.OUT)
    
    cookies = loadCookies()
    occupied_status = open(status_filename, 'r').read()
    occupied_since = open(timestamp_filename, 'r').read()
    params = {'sensor_uuid': cookies['sensor_uuid']}
    data = {
        'occ_status': occupied_status,
        # 'occ_status': '1',
	'occ_since': occupied_since,
        # 'occ_since': datetime.datetime.now(),
        # 'occ_license': occupied_license,
        'occ_license': '4AME671',
        #'csrfmiddlewaretoken': cookies['csrftoken']
    }
    
    r = requests.post(
        base_url+"sensor/",
        params = params,
        data = data,
        cookies = cookies,
    )

    printResponse(r)
    #if(occupied_status == '0'):
	#GPIO.output(COLOR, False)
    #if(occupied_status == '1'):
	#GPIO.output(COLOR, True)	

def sensor_getUUID_GET():
    params = {'mac_addr': uuid.getnode()}
    r = requests.get(base_url+'sensor/getUUID/', params = params)
    #print(r.cookies['csrftoken'])
    saveCookies(r.cookies)
    
    f = open(uuid_filename, 'w')
    sensor_uuid_hex = uuid.UUID(r.cookies['sensor_uuid']).hex
    
    s = str(sensor_uuid_hex)
    new_hex = " ".join(s[i:i+2] for i in range(0, len(s),2))
    #hex_s = new_hex[0:12] + new_hex[30:]
    #print(hex_s)
    f.write(new_hex)
    f.close()

    printResponse(r)

#######################COOKIE CODE#############################

def saveCookies(requests_cookiejar):
    with open(cookie_filename, 'wb') as f:
        pickle.dump(requests_cookiejar, f)


def loadCookies():
    with open(cookie_filename, 'rb') as f:
        return pickle.load(f)


def printResponse(r):
    print("------ GET: Status = " + str(r.status_code) + " -----")
    print('----------- Headers ----------')
    for key,val in r.headers.items():
        print key, " : ", val
    print('------------ Text ------------')
    print(r.text)
    print('------------------------------\n\n')
